wilhelmzeuschner/MPPT_Solar_KiCAD_Rev2.1/doc/code_doc/html/mppt__control__algo_8cpp_a3b2fd1876a11e9cd4bce8aa751742aaa_cgraph.png

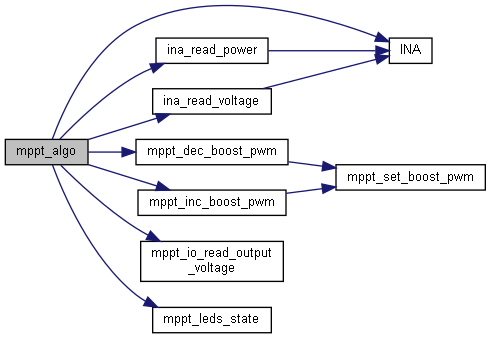
doc/code_doc/html/mppt__control__algo_8cpp_a3b2fd1876a11e9cd4bce8aa751742aaa_cgraph.png
