wilhelmzeuschner/MPPT_Solar_KiCAD_Rev2.1/doc/code_doc/html/mppt__control__algo_8cpp_adab9bfdfc6d27973c36659b5cfcda55f_cgraph.png

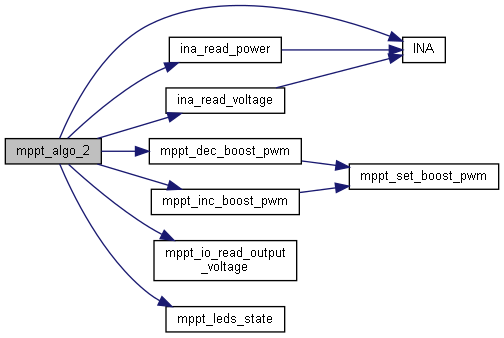
doc/code_doc/html/mppt__control__algo_8cpp_adab9bfdfc6d27973c36659b5cfcda55f_cgraph.png
