wilhelmzeuschner/MPPT_Solar_KiCAD_Rev2.1/doc/code_doc/html/mppt__main_8cpp_a4fc01d736fe50cf5b977f755b675f11d_cgraph.png

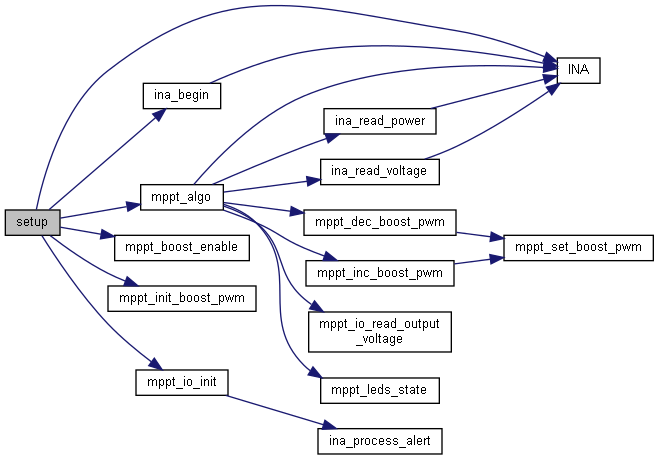
doc/code_doc/html/mppt__main_8cpp_a4fc01d736fe50cf5b977f755b675f11d_cgraph.png
