wilhelmzeuschner/MPPT_Solar_KiCAD_Rev2.1/doc/code_doc/html/mppt__main_8cpp_a04361e44df72145163c3b97c29cf31c6_icgraph.png

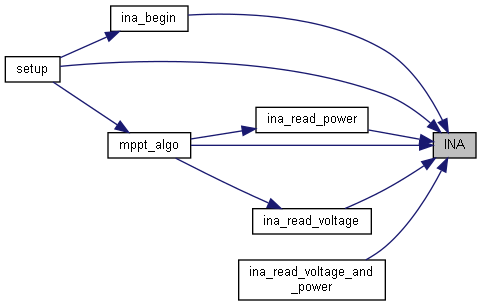
doc/code_doc/html/mppt__main_8cpp_a04361e44df72145163c3b97c29cf31c6_icgraph.png
