wilhelmzeuschner/MPPT_Solar_KiCAD_Rev2.1/doc/latex/img/case/case_param.png

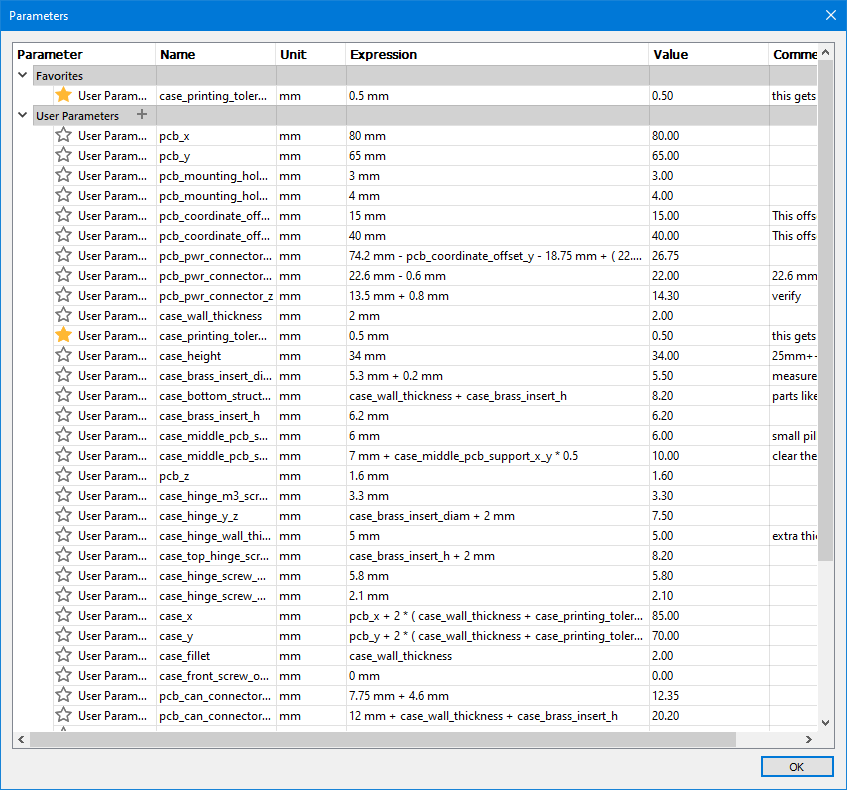
doc/latex/img/case/case_param.png
