wilhelmzeuschner/MPPT_Solar_KiCAD_Rev2.1/doc/latex/img/case/case_render.PNG

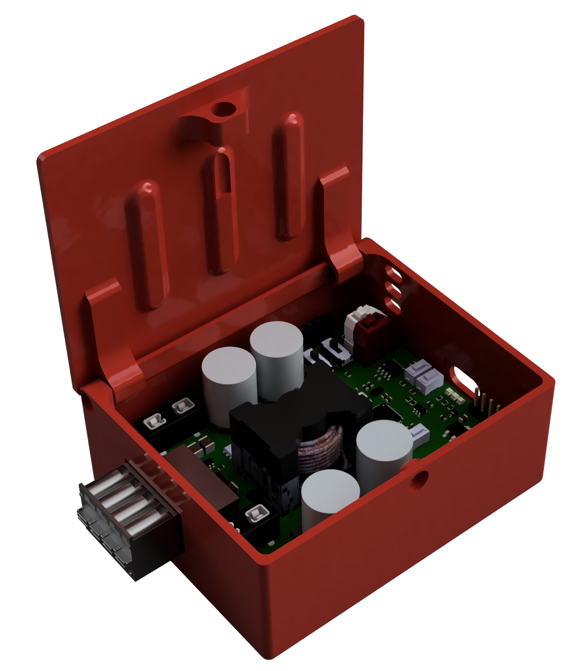
doc/latex/img/case/case_render.PNG
