wilhelmzeuschner/MPPT_Solar_KiCAD_Rev2.1/doc/latex/img/draw/MPPT_Allgemein.drawio.png

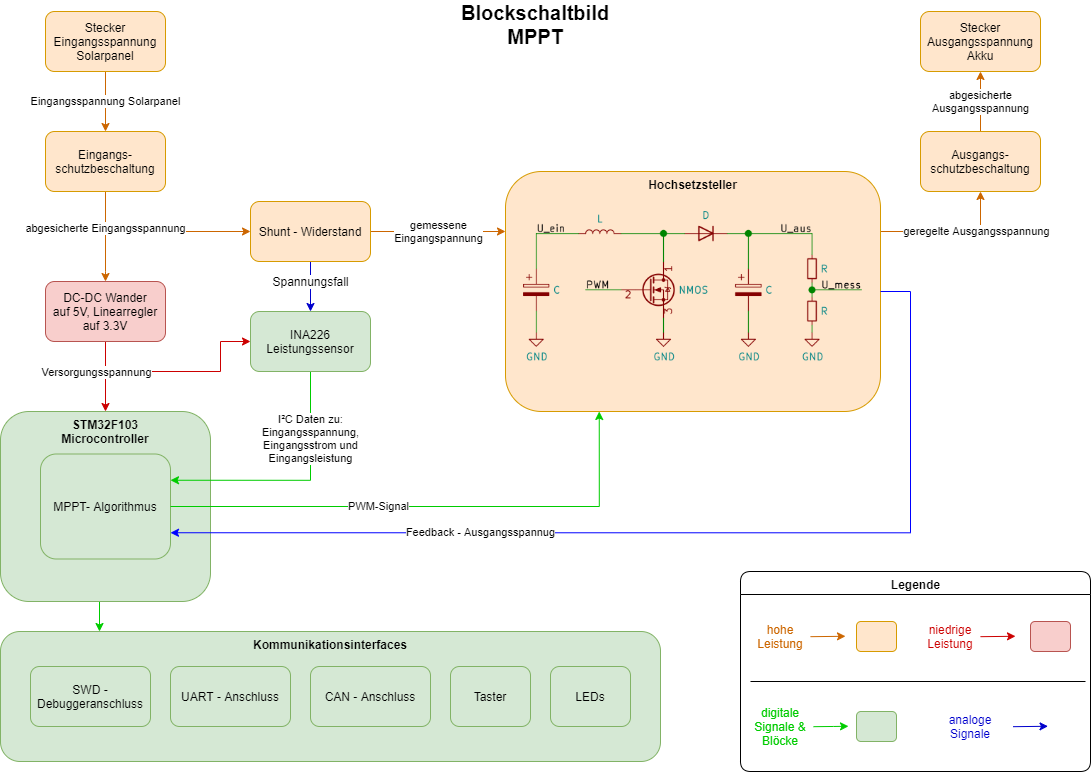
doc/latex/img/draw/MPPT_Allgemein.drawio.png
