wilhelmzeuschner/MPPT_Solar_KiCAD_Rev2.1/doc/latex/img/draw/pcb_pdf/Screenshot 2022-02-08 210044.jpg

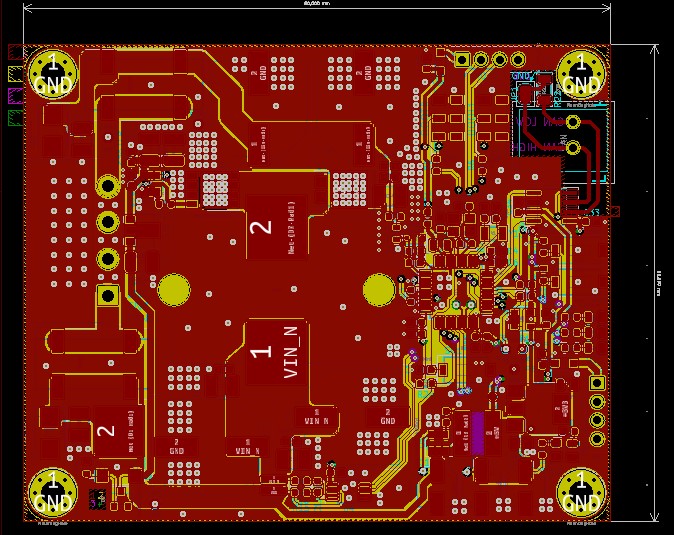
doc/latex/img/draw/pcb_pdf/Screenshot 2022-02-08 210044.jpg
