wilhelmzeuschner/MPPT_Solar_KiCAD_Rev2.1/doc/latex/img/end/end_no_stock_many.png

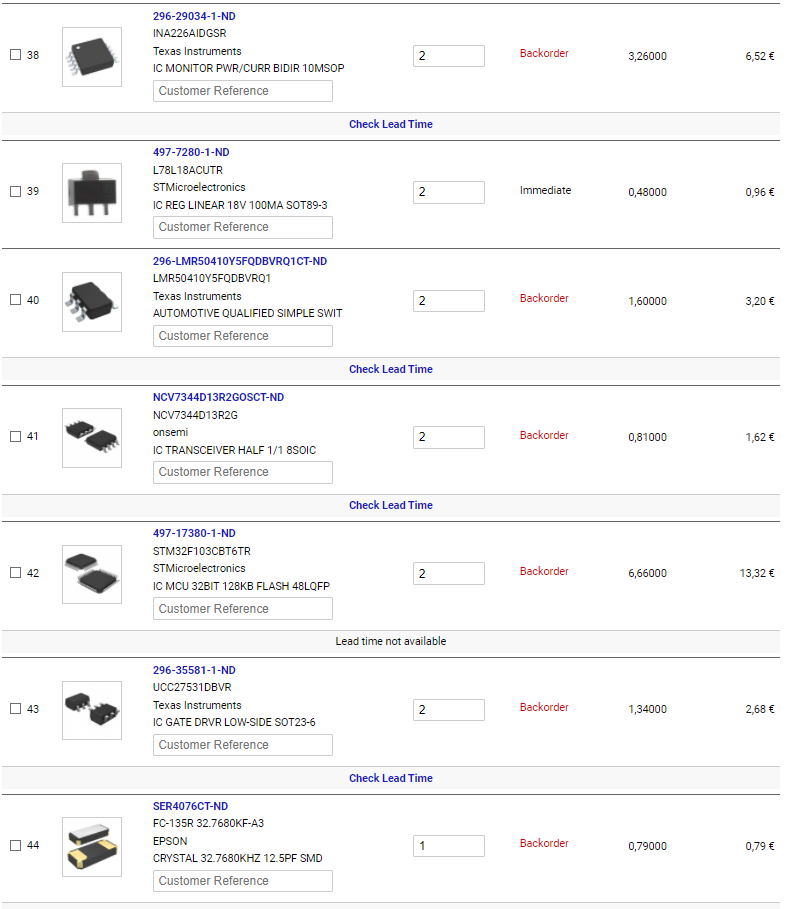
doc/latex/img/end/end_no_stock_many.png
