wilhelmzeuschner/MPPT_Solar_KiCAD_Rev2.1/doc/latex/img/end/MPPT_Solar_KiCAD_render.png

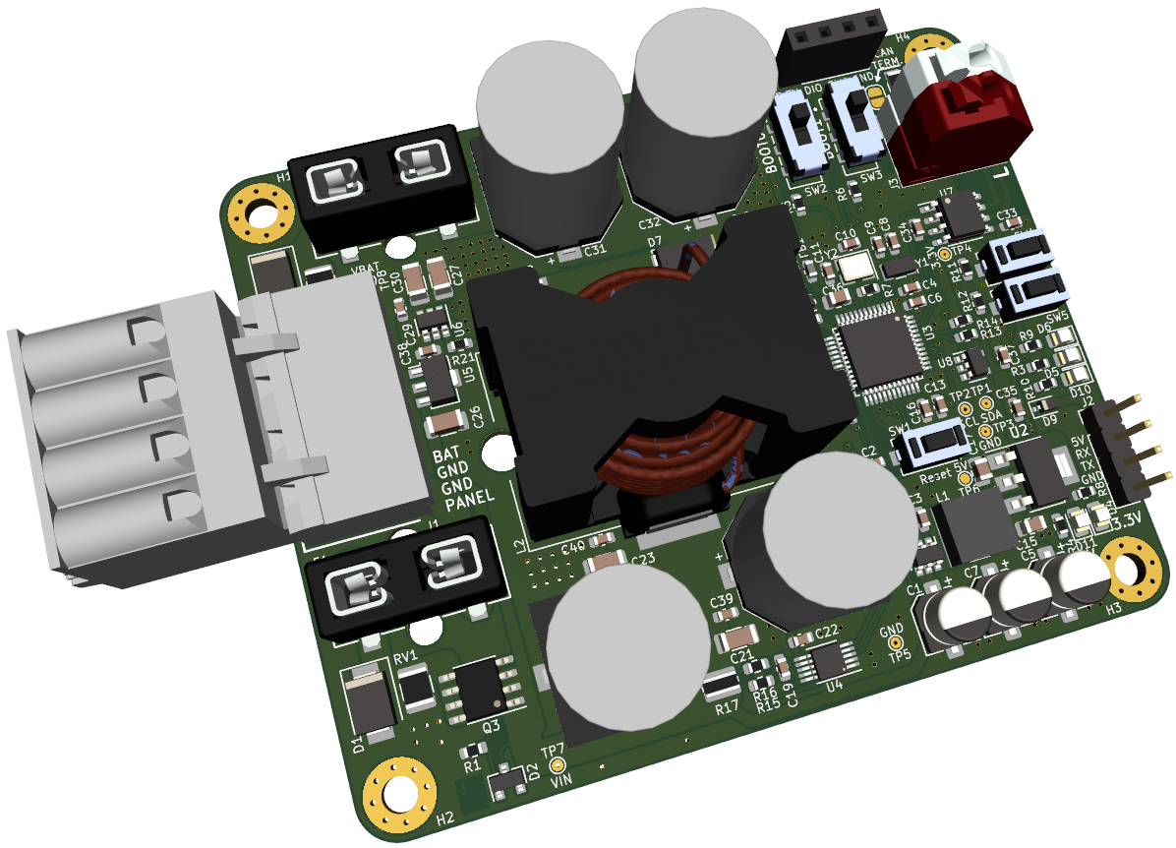
doc/latex/img/end/MPPT_Solar_KiCAD_render.png
