wilhelmzeuschner/MPPT_Solar_KiCAD_Rev2.1/doc/latex/img/intro/IMG_20211028_193830.jpg

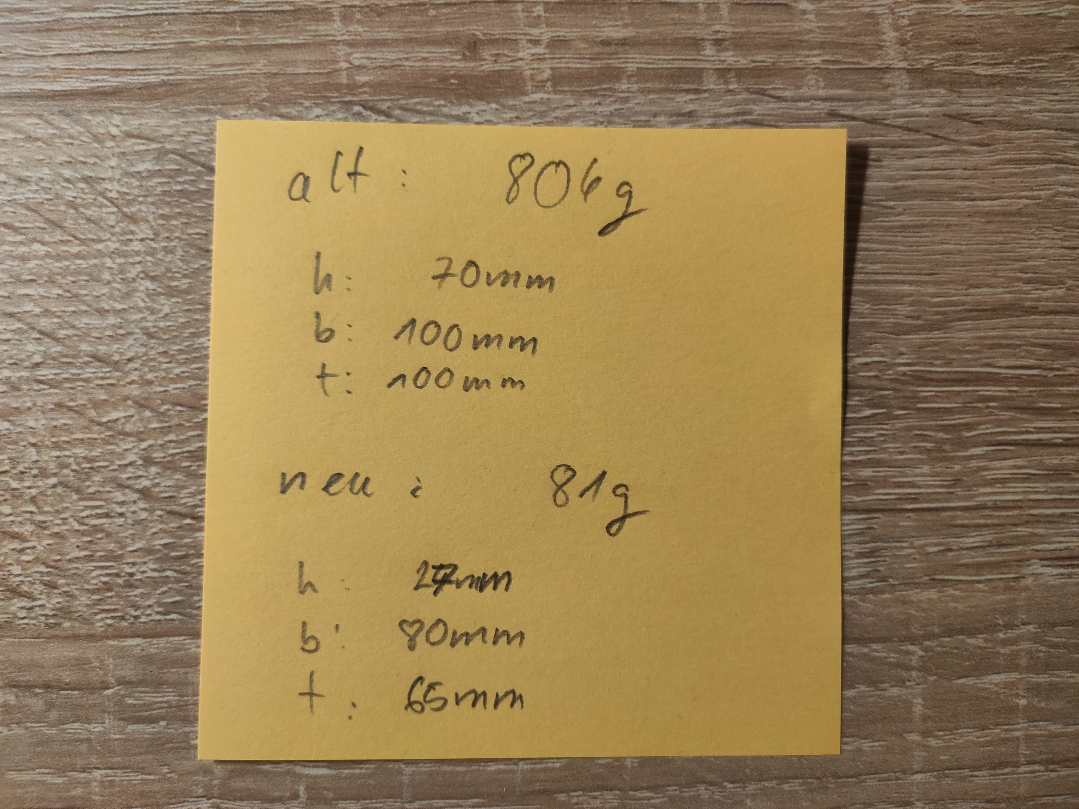
doc/latex/img/intro/IMG_20211028_193830.jpg
