wilhelmzeuschner/MPPT_Solar_KiCAD_Rev2.1/doc/latex/img/intro/new_bottom.jpg

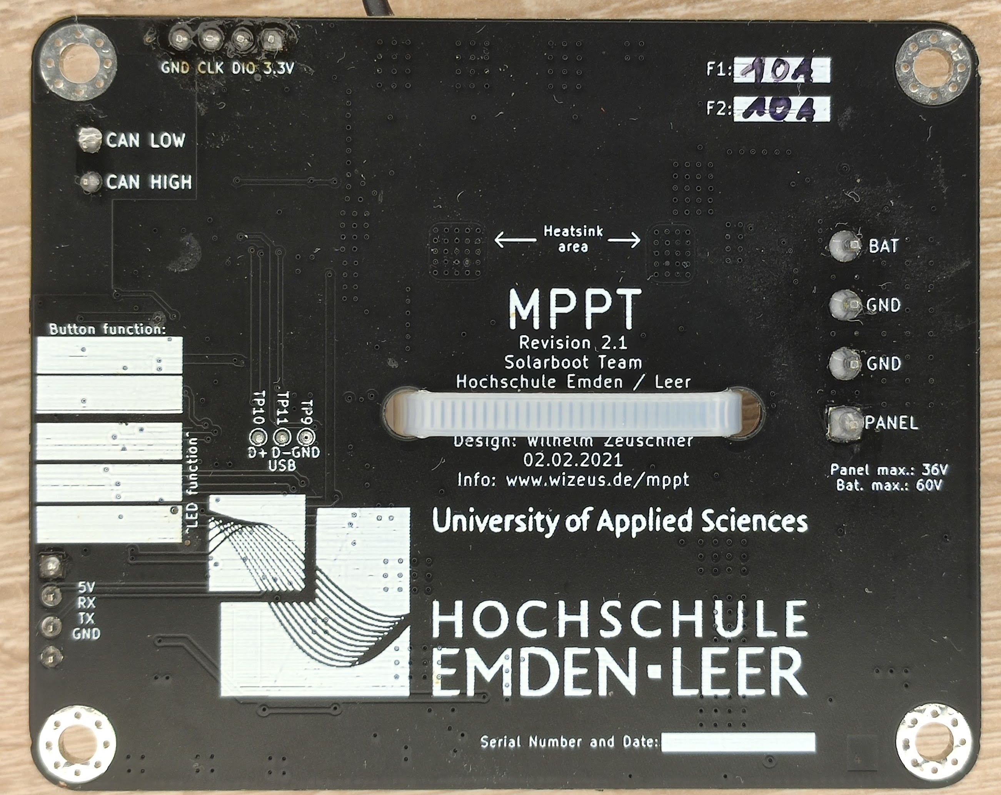
doc/latex/img/intro/new_bottom.jpg
