wilhelmzeuschner/MPPT_Solar_KiCAD_Rev2.1/doc/latex/img/intro/new_top.jpg

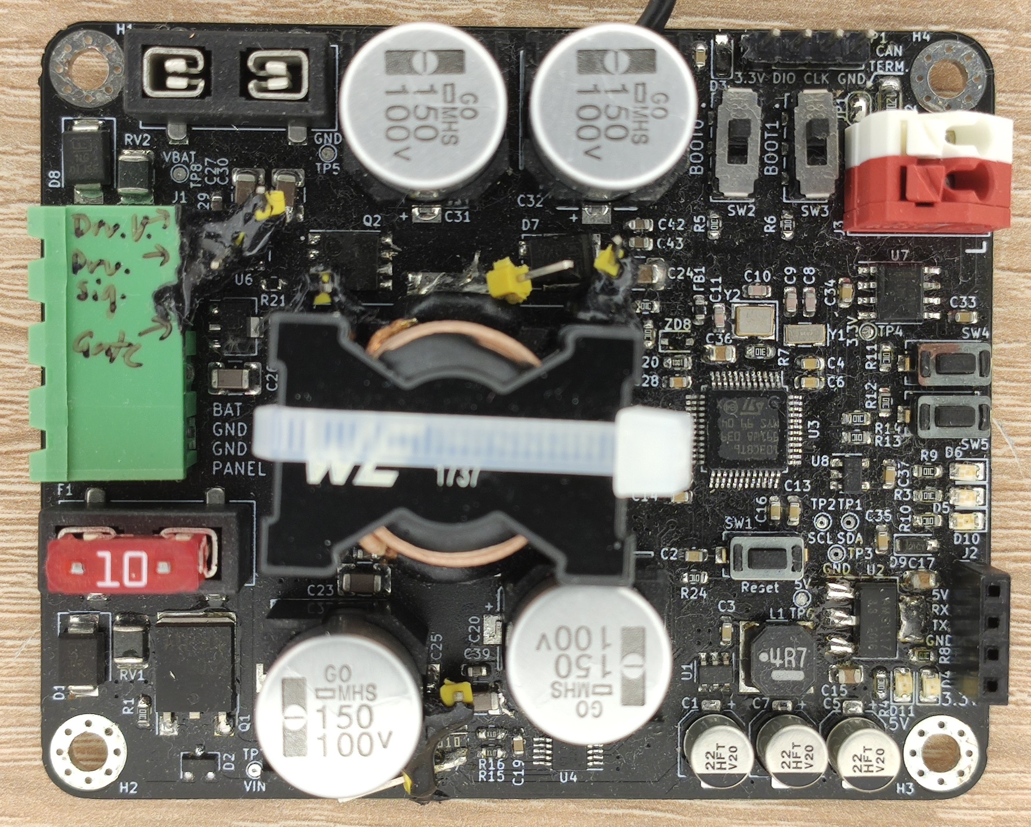
doc/latex/img/intro/new_top.jpg
