wilhelmzeuschner/MPPT_Solar_KiCAD_Rev2.1/doc/latex/img/meas/meas_efficiency_0_to1_graph.png

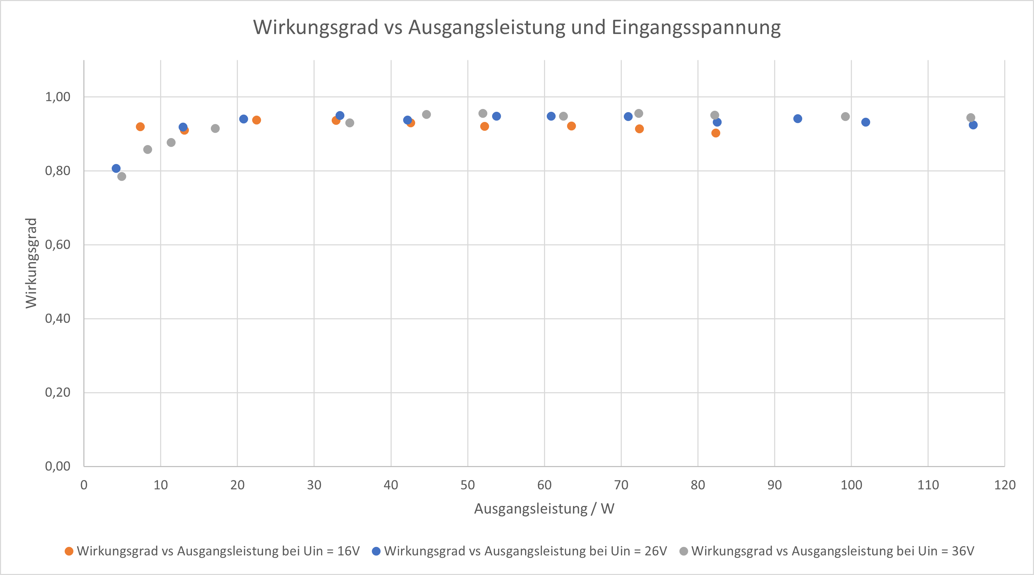
doc/latex/img/meas/meas_efficiency_0_to1_graph.png
