wilhelmzeuschner/MPPT_Solar_KiCAD_Rev2.1/doc/latex/img/meas/meas_max_power_no_outline.png

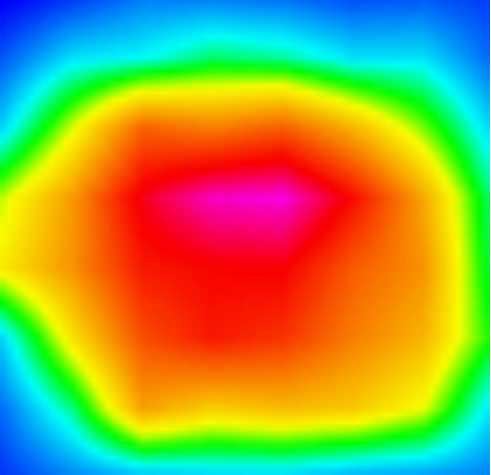
doc/latex/img/meas/meas_max_power_no_outline.png
