wilhelmzeuschner/MPPT_Solar_KiCAD_Rev2.1/doc/latex/img/pcb/layout segments/pcb_layout_5v_3v.png

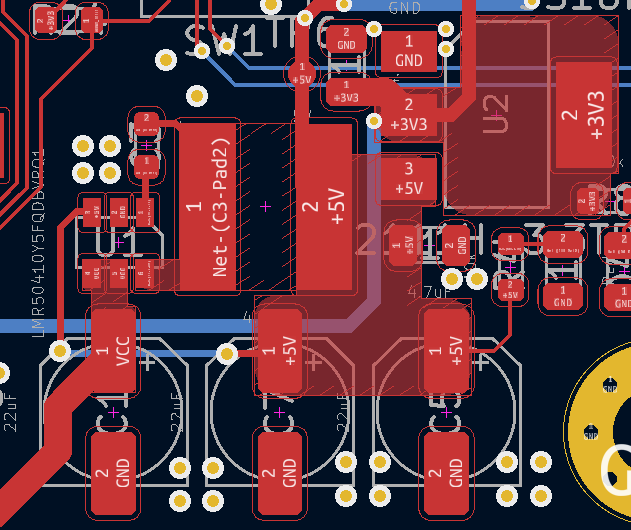
doc/latex/img/pcb/layout segments/pcb_layout_5v_3v.png
