wilhelmzeuschner/MPPT_Solar_KiCAD_Rev2.1/doc/latex/img/pcb/pcb_front_cu_fill.png

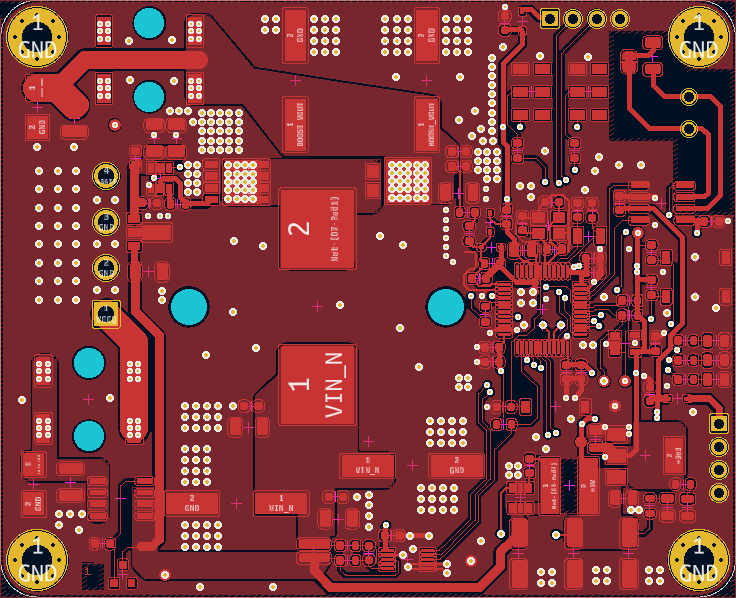
doc/latex/img/pcb/pcb_front_cu_fill.png
