wilhelmzeuschner/MPPT_Solar_KiCAD_Rev2.1/doc/latex/img/pcb/pcb_in1_cu.png

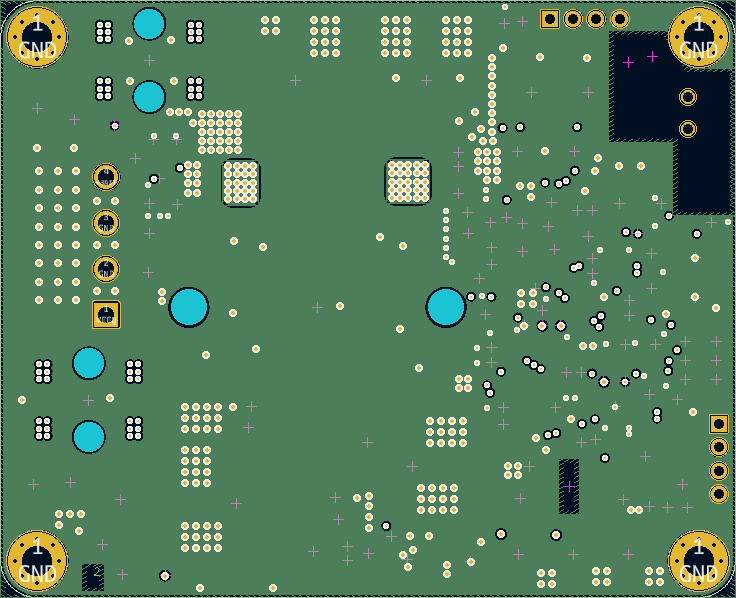
doc/latex/img/pcb/pcb_in1_cu.png
