wilhelmzeuschner/MPPT_Solar_KiCAD_Rev2.1/doc/latex/img/pcb/pcb_render_bottom.png

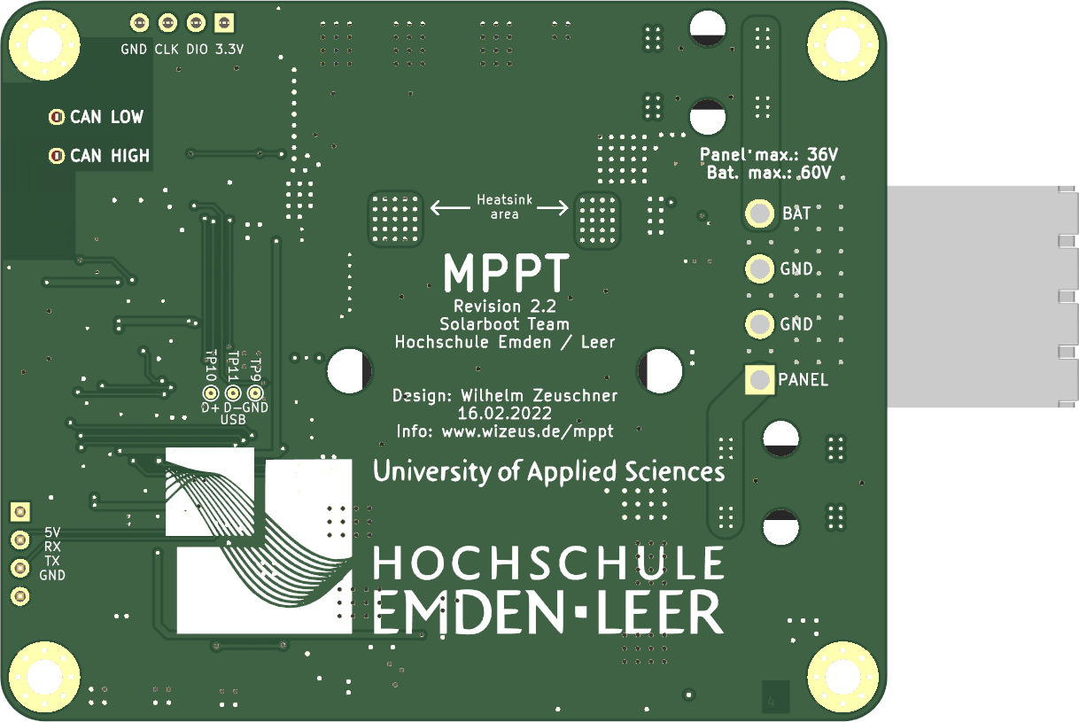
doc/latex/img/pcb/pcb_render_bottom.png
