wilhelmzeuschner/MPPT_Solar_KiCAD_Rev2.1/doc/latex/img/schematics/all sections of the project/schem_block_overview.png

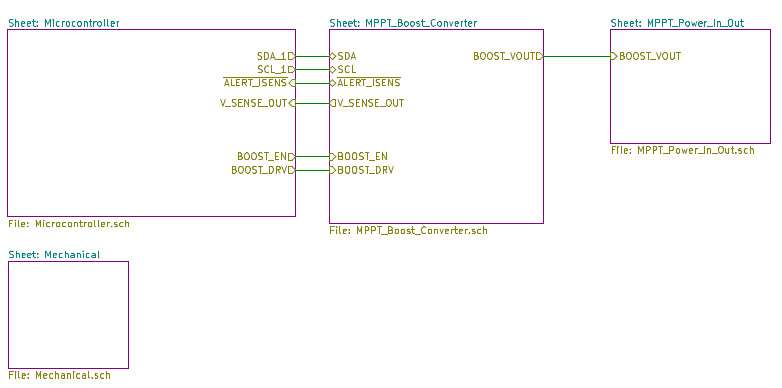
doc/latex/img/schematics/all sections of the project/schem_block_overview.png
