wilhelmzeuschner/MPPT_Solar_KiCAD_Rev2.1/doc/latex/img/schematics/boost_converter_example/boost_converter.png

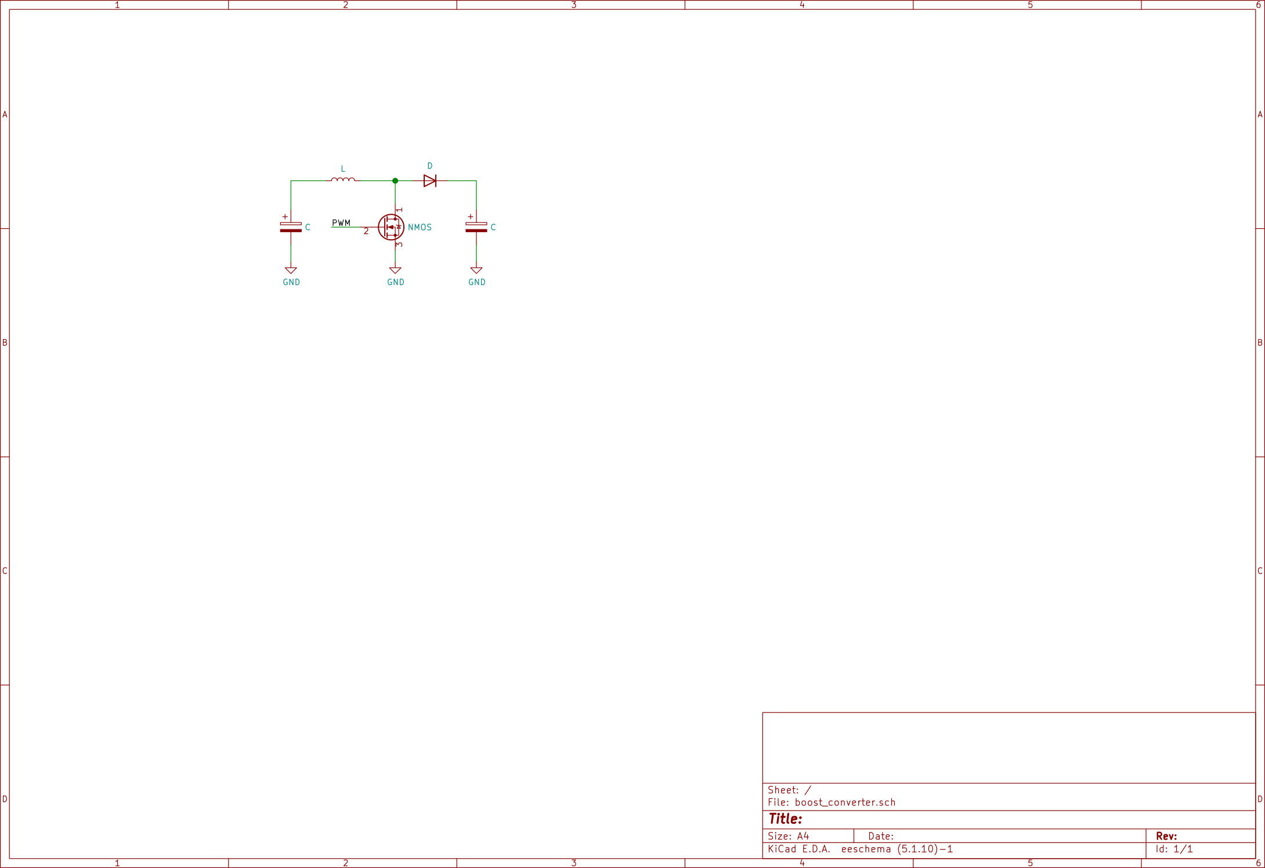
doc/latex/img/schematics/boost_converter_example/boost_converter.png
