wilhelmzeuschner/MPPT_Solar_KiCAD_Rev2.1/doc/latex/img/schematics/boost_converter_example/g2467.png

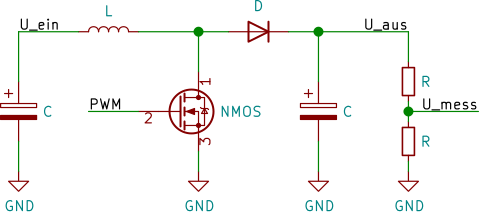
doc/latex/img/schematics/boost_converter_example/g2467.png
