wilhelmzeuschner/MPPT_Solar_KiCAD_Rev2.1/doc/latex/img/schematics/sim_filter.png

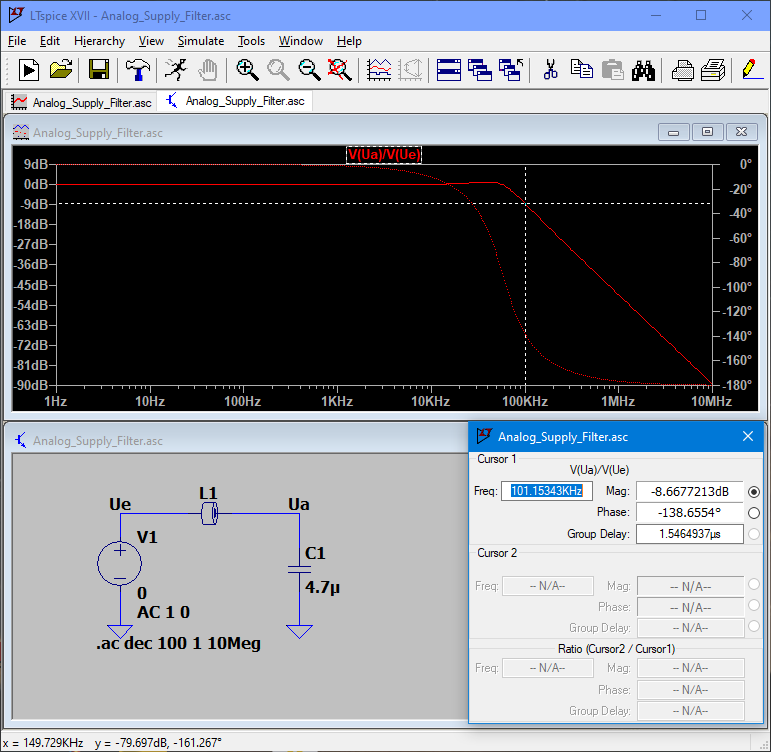
doc/latex/img/schematics/sim_filter.png
