wilhelmzeuschner/MPPT_Solar_KiCAD_Rev2.1/doc/latex/img/sim/sim_output_reverse_schem.jpg

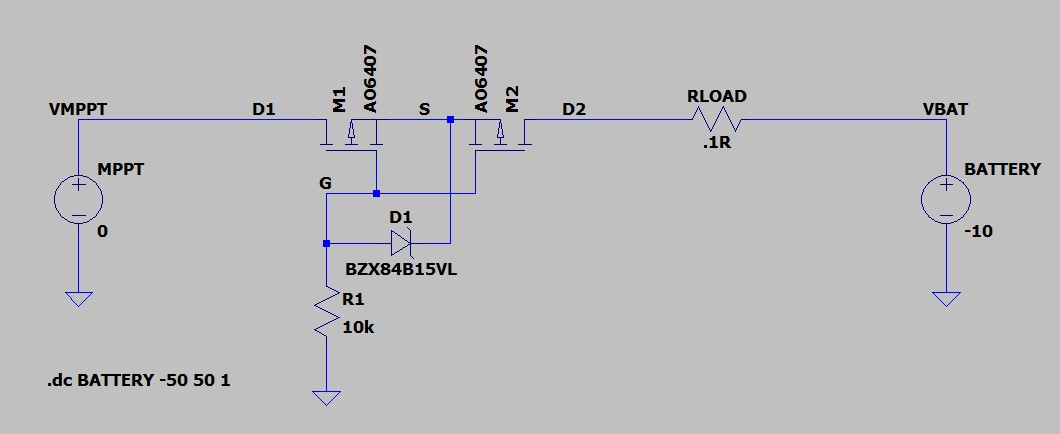
doc/latex/img/sim/sim_output_reverse_schem.jpg
