wilhelmzeuschner/MPPT_Solar_KiCAD_Rev2.1/doc/latex/img/sw/mppt_algo_diagram.png

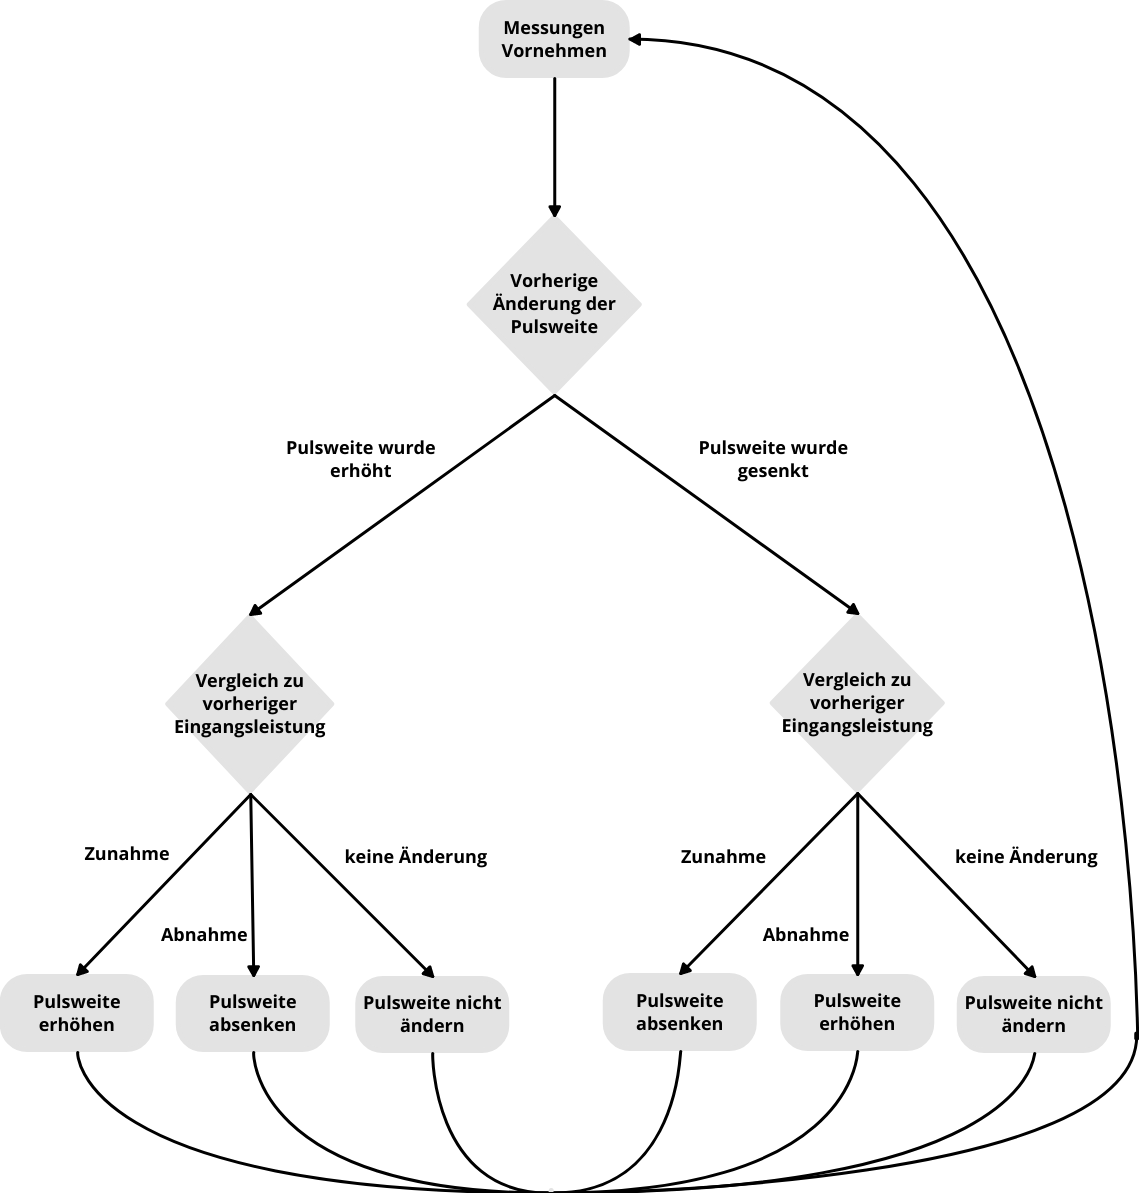
doc/latex/img/sw/mppt_algo_diagram.png
