wilhelmzeuschner/MPPT_Solar_KiCAD_Rev2.1/doc/latex/img/sw/sw_desk_overview.jpg

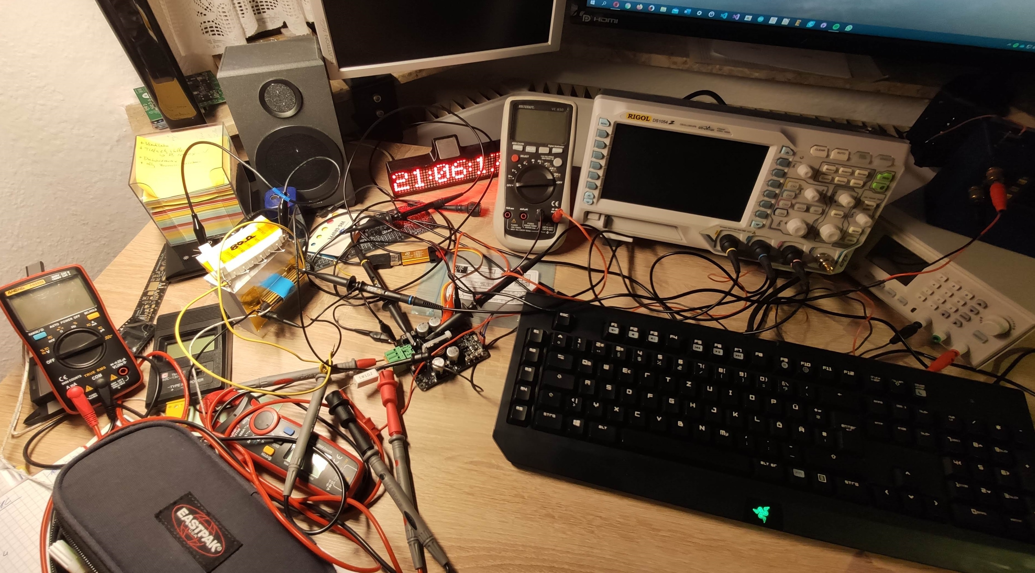
doc/latex/img/sw/sw_desk_overview.jpg
