wilhelmzeuschner/MPPT_Solar_KiCAD_Rev2.1/doc/latex/img/sw/sw_git_overview.png

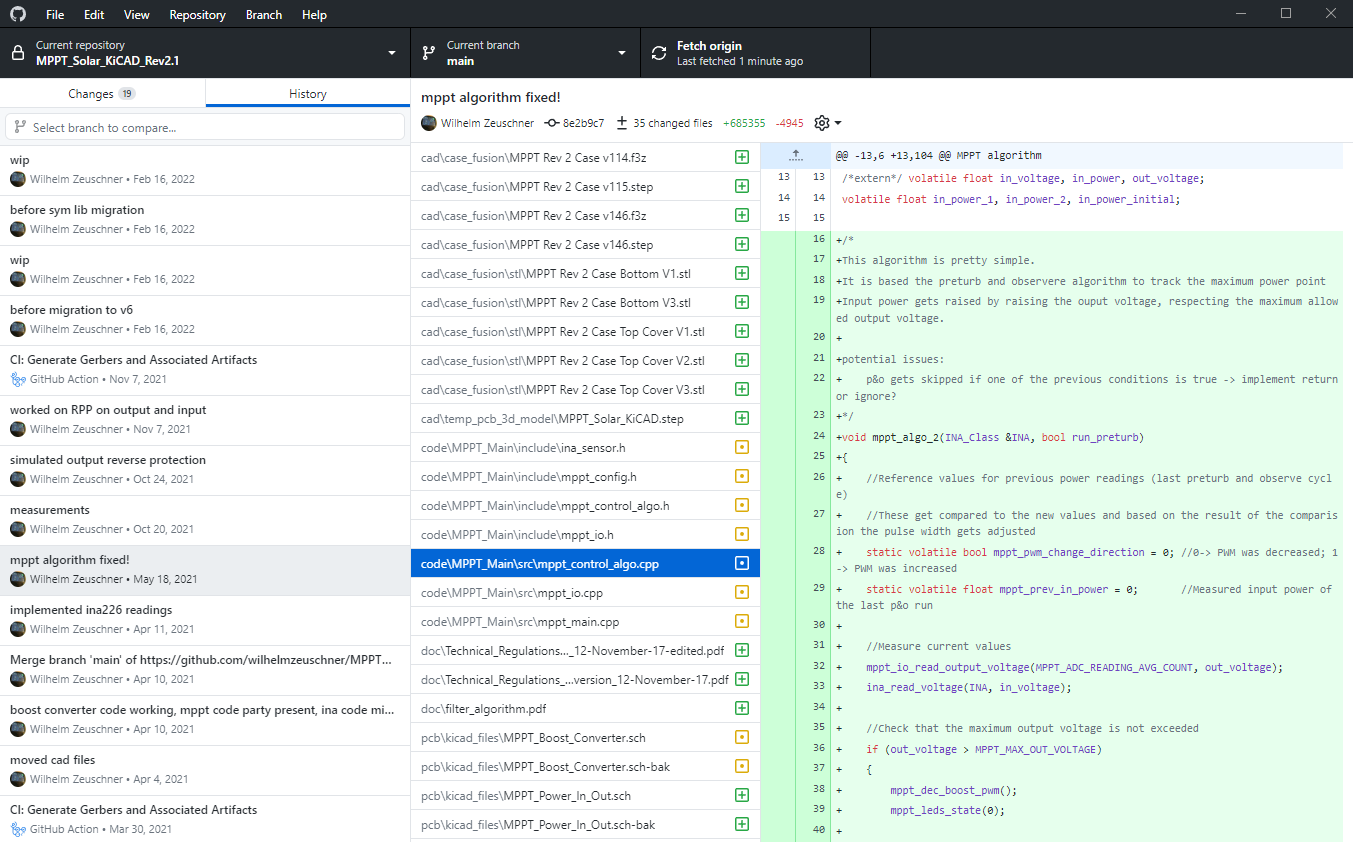
doc/latex/img/sw/sw_git_overview.png
