wilhelmzeuschner/MPPT_Solar_KiCAD_Rev2.1/doc/latex/img/sw/sw_mppt_wiki_markers.png

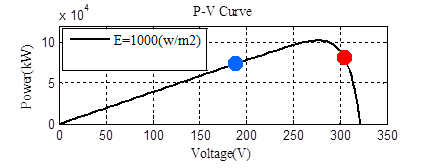
doc/latex/img/sw/sw_mppt_wiki_markers.png
