wilhelmzeuschner/MPPT_Solar_KiCAD_Rev2.1/pcb/export/MPPT_Solar_KiCAD-top.png

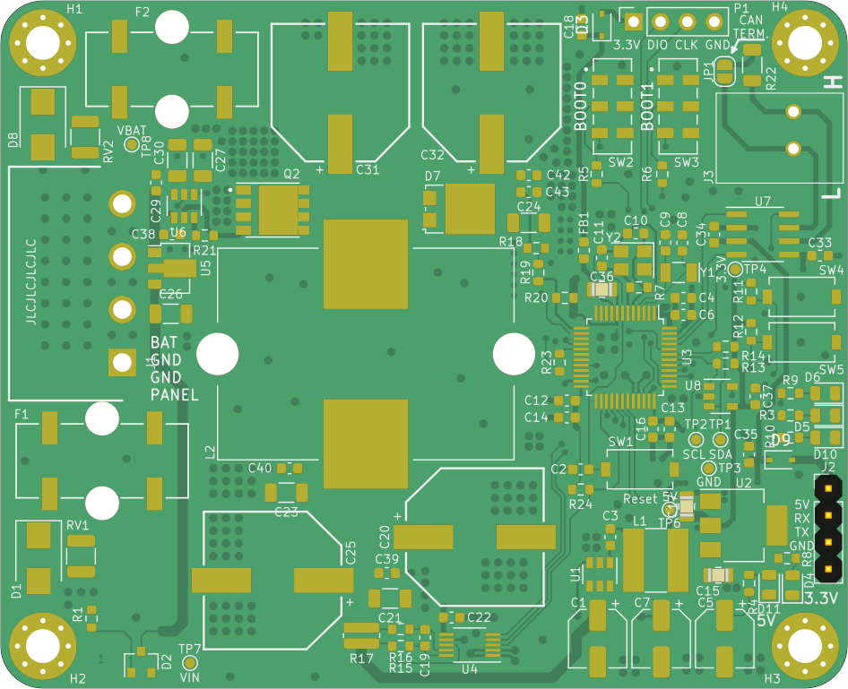
pcb/export/MPPT_Solar_KiCAD-top.png
