wilhelmzeuschner/MPPT_Solar_KiCAD_Rev2.1/doc/latex/img/pcb/pcb_paste_components.jpg

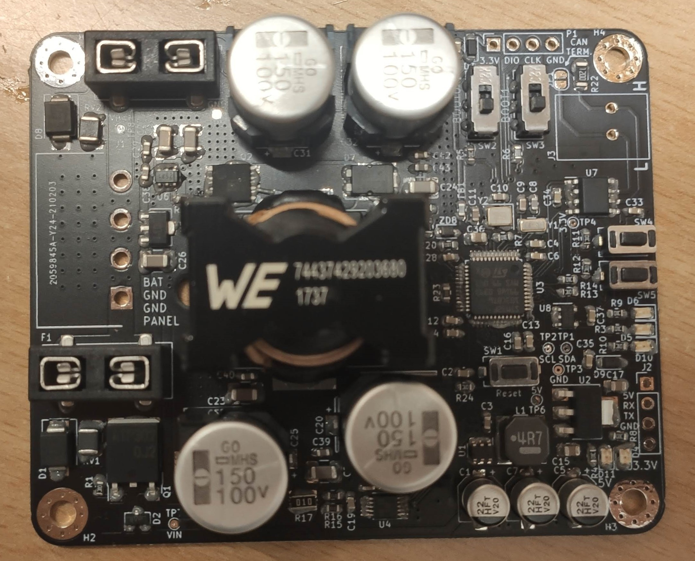
doc/latex/img/pcb/pcb_paste_components.jpg
