wilhelmzeuschner/MPPT_Solar_KiCAD_Rev2.1/doc/latex/img/pcb/pcb_render_top_no_components.png

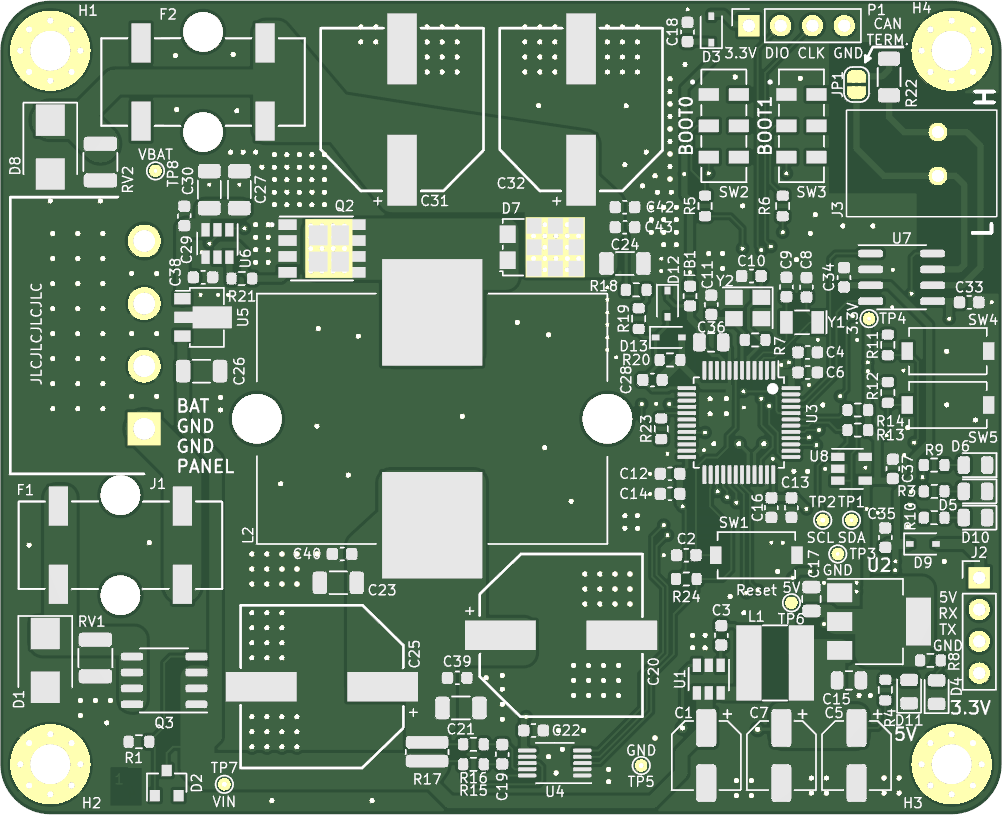
doc/latex/img/pcb/pcb_render_top_no_components.png
