wilhelmzeuschner/MPPT_Solar_KiCAD_Rev2.1/doc/latex/img/pcb/pcb_solder_paste.jpg

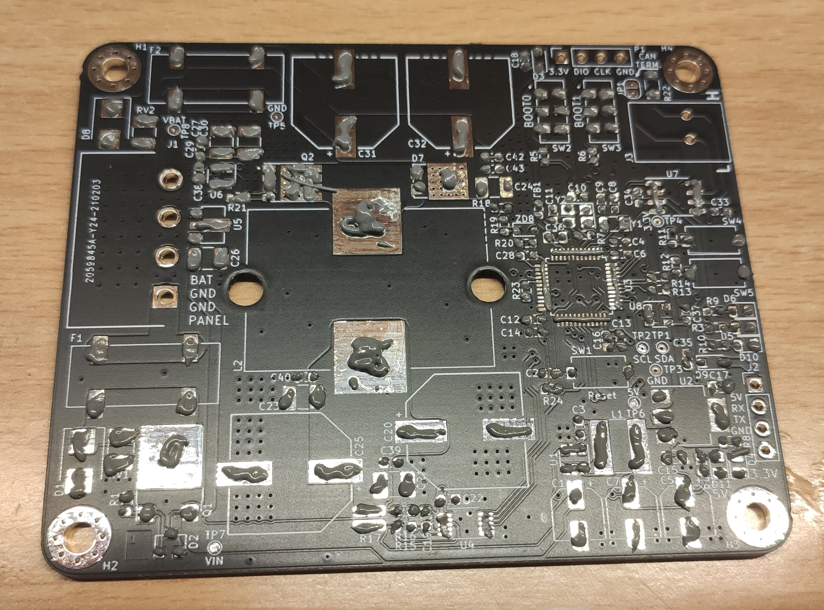
doc/latex/img/pcb/pcb_solder_paste.jpg
