wilhelmzeuschner/MPPT_Solar_KiCAD_Rev2.1/validation/Scope captures/algorithm check/DS1Z_QuickPrint9.png

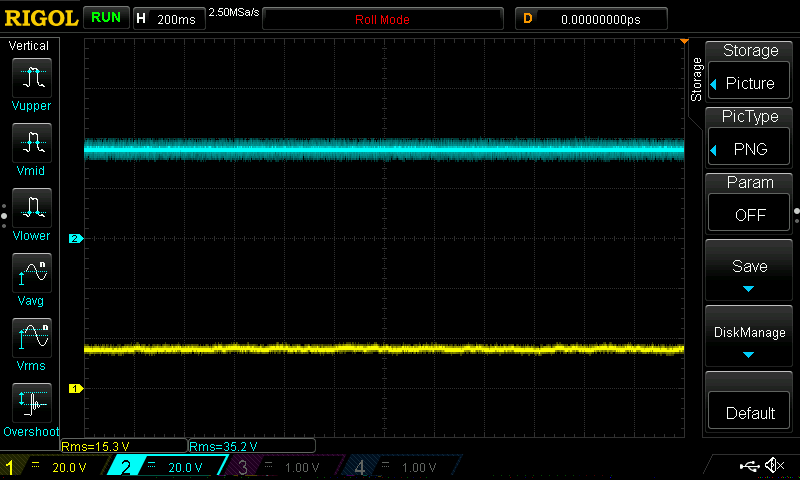
validation/Scope captures/algorithm check/DS1Z_QuickPrint9.png
