wilhelmzeuschner/MPPT_Solar_KiCAD_Rev2.1/validation/Scope captures/algorithm check/DS1Z_QuickPrint14.png

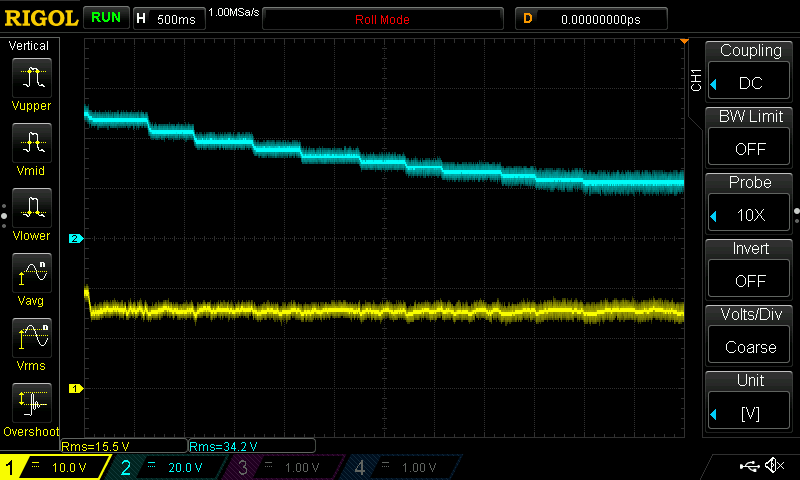
validation/Scope captures/algorithm check/DS1Z_QuickPrint14.png
