wilhelmzeuschner/MPPT_Solar_KiCAD_Rev2.1/validation/Scope captures/input step/falling input voltage/InputStepResponseStepFrom36VStepTo16VPout=20W.png

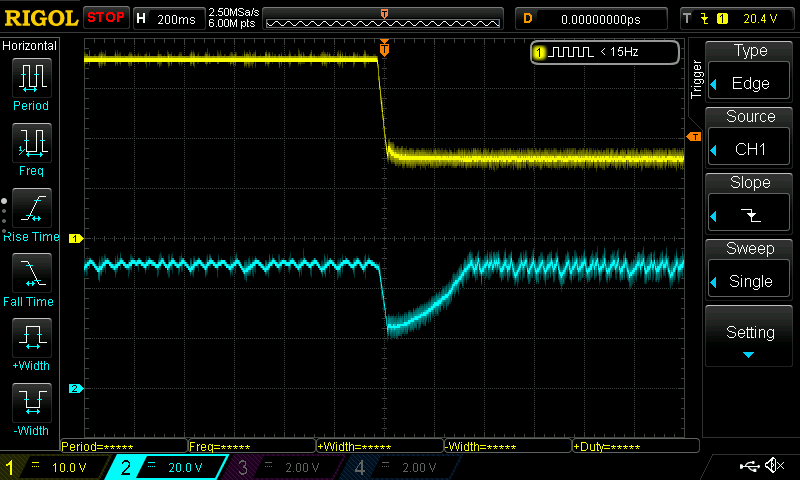
validation/Scope captures/input step/falling input voltage/InputStepResponseStepFrom36VStepTo16VPout=20W.png
