wilhelmzeuschner/MPPT_Solar_KiCAD_Rev2.1/validation/Scope captures/input step/rising voltage/InputStepResponseStepFrom16VStepTo36VPout=0W.png

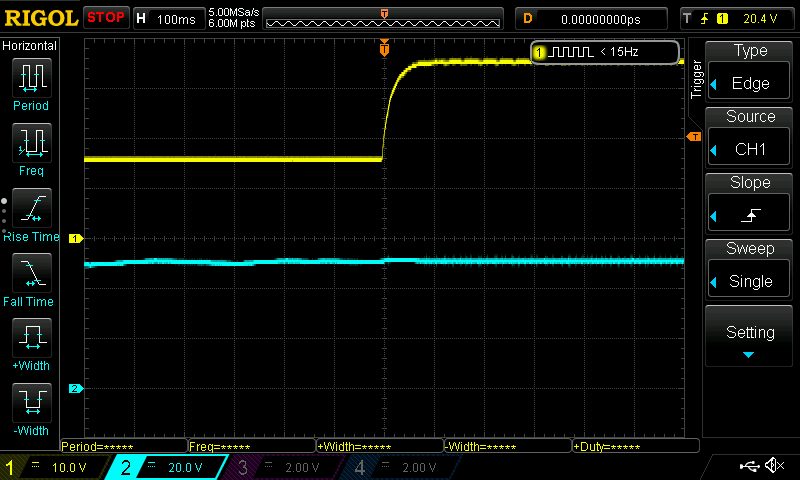
validation/Scope captures/input step/rising voltage/InputStepResponseStepFrom16VStepTo36VPout=0W.png
