wilhelmzeuschner/MPPT_Solar_KiCAD_Rev2.1/validation/Scope captures/output step/OutputStepVin =36VVout =50VPout=20W.png

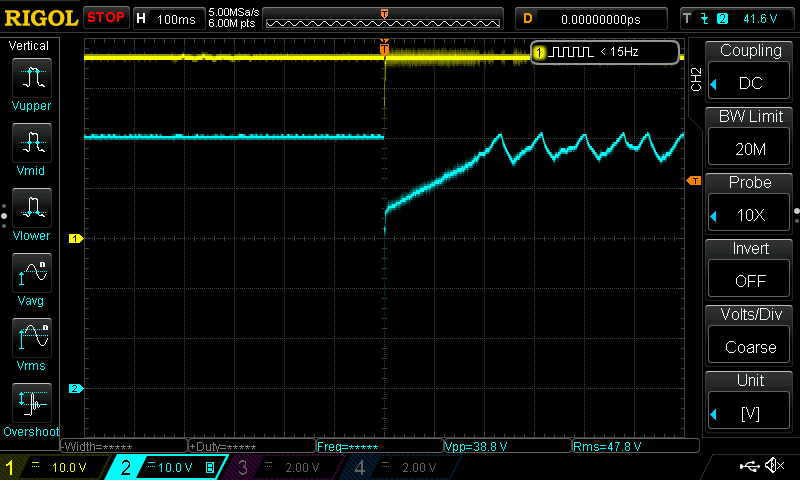
validation/Scope captures/output step/OutputStepVin =36VVout =50VPout=20W.png
