wilhelmzeuschner/MPPT_Solar_KiCAD_Rev2.1/doc/latex/img/draw/MPPT Algo Verification.drawio.png

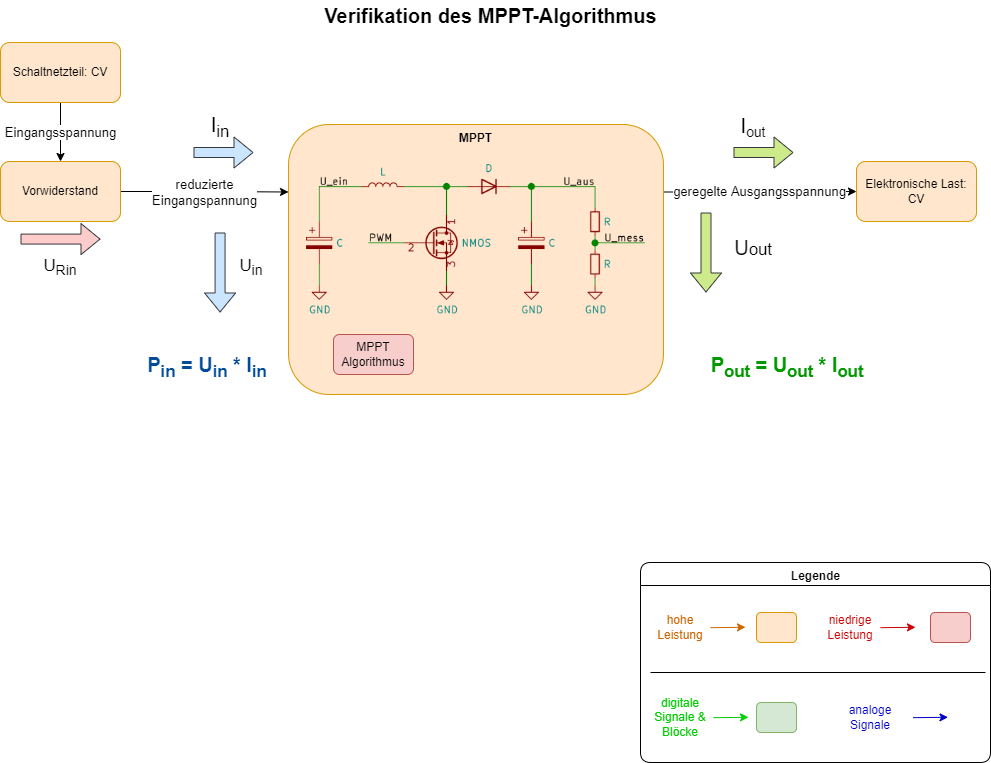
doc/latex/img/draw/MPPT Algo Verification.drawio.png
