wilhelmzeuschner/MPPT_Solar_KiCAD_Rev2.1/doc/latex/img/meas/meas_mppt_verification_desk_setup.jpg

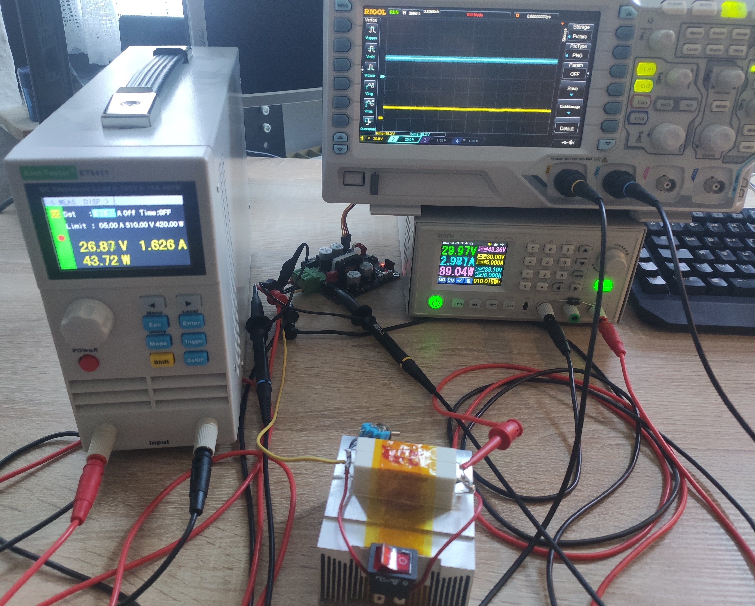
doc/latex/img/meas/meas_mppt_verification_desk_setup.jpg
