wilhelmzeuschner/MPPT_Solar_KiCAD_Rev2.1/validation/Scope captures/no load/nothing at all.png

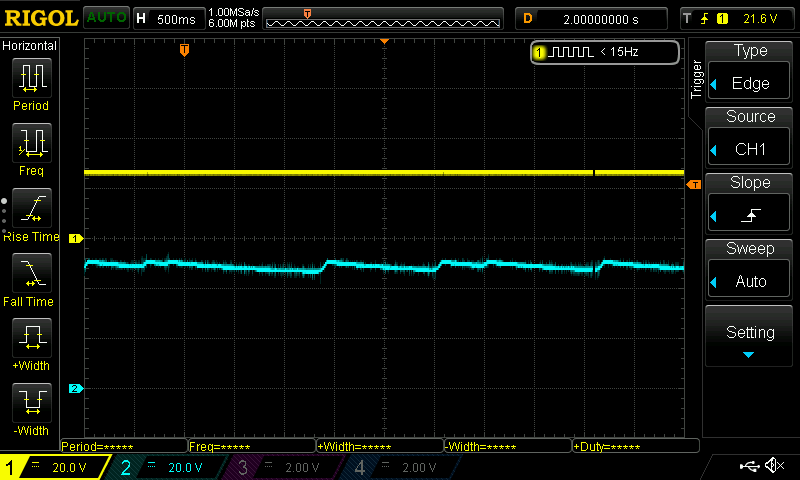
validation/Scope captures/no load/nothing at all.png
