wilhelmzeuschner/MPPT_Solar_KiCAD_Rev2.1/validation/Scope captures/output ripple/OutputRippleVin=36VPout=40W.png

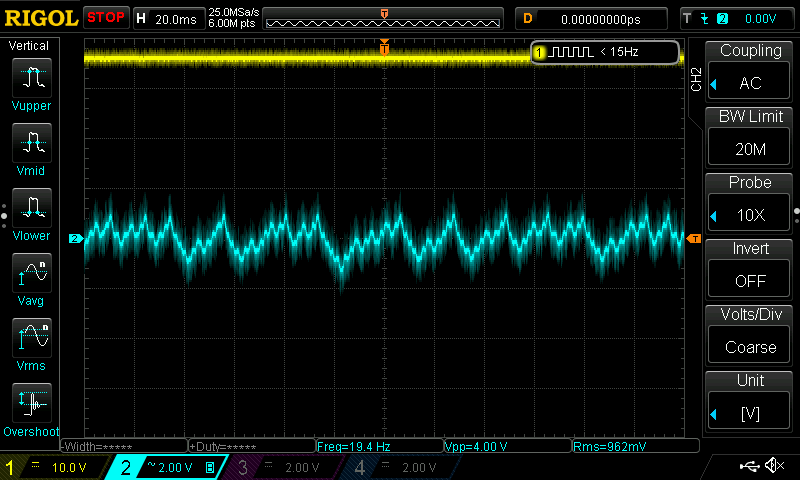
validation/Scope captures/output ripple/OutputRippleVin=36VPout=40W.png
