wilhelmzeuschner/MPPT_Solar_KiCAD_Rev2.1/validation/Scope captures/vin too low/vin_too_low.png

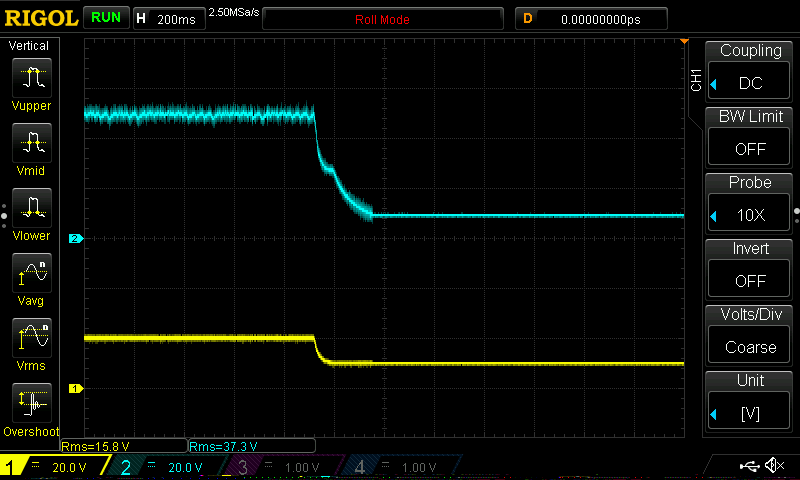
validation/Scope captures/vin too low/vin_too_low.png
