wilhelmzeuschner/MPPT_Solar_KiCAD_Rev2.1/sim/Analog_Supply_Filter/Analog_Supply_Filter.asc

C1: cap; 4.7µ
L1: FerriteBead; 1.6µ; Rser=.6
V1: voltage; 0; AC 1 0
Named nets: Ue, Ua, 0
.ac dec 100 1 10Meg
