wilhelmzeuschner/MPPT_Solar_KiCAD_Rev2.1/sim/OutputReversePolarityProtection/OutputReversePolarityProtection.asc

BATTERY: voltage; 40
D1: zener; BZX84B15VL
M1: pmos
MPPT: voltage; 0
R1: res; 10k
RLOAD: res; 1R
Named nets: 0, VMPPT, VBAT, G, S, D
.dc BATTERY -50 50 1 ;.dc MPPT 0 50 1 BATTERY 50 0 1
