wilhelmzeuschner/MPPT_Solar_KiCAD_Rev2.1/sim/OutputReversePolarityProtection/OutputReversePolarityProtectionBackToBack.asc

BATTERY: voltage; 10
D1: zener; BZX84B15VL
M1: pmos; AO6407
M2: pmos; AO6407
MPPT: voltage; 0
R1: res; 10
R2: res; 10k
R3: res; 10
RLOAD: res; 10
Named nets: 0, VMPPT, VBAT, G, S, D2, D1
.dc MPPT -50 50 1
